google/makerspace-auth/docs/tool-connection/epilog_mini_24/plates/two_box_mount.png

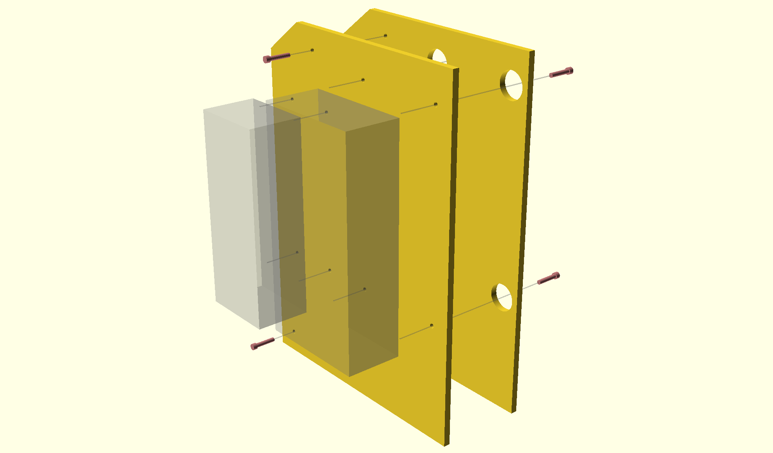
docs/tool-connection/epilog_mini_24/plates/two_box_mount.png
