google/makerspace-auth/docs/tool-connection/epilog_mini_24/plates/one_box_mount_inner.scad

include <one_box_mount_lib.scad>
Inner();
