google/makerspace-auth/docs/tool-connection/epilog_mini_24/plates/one_box_mount_lid_hole_template.scad

include <one_box_mount_lib.scad>
LidHoleTemplate();
