google/makerspace-auth/docs/tool-connection/epilog_mini_24/plates/two_box_mount_demo.scad

include <two_box_mount_lib.scad>
rotate([90,0,0]) Exploded();
