google/makerspace-auth/docs/tool-connection/epilog_mini_24/plates/two_box_mount_inner.scad

include <two_box_mount_lib.scad>
Inner();
