google/makerspace-auth/docs/tool-connection/epilog_mini_24/plates/two_box_mount_outer.scad

include <two_box_mount_lib.scad>
Outer();
