google/makerspace-auth/docs/tool-connection/epilog_mini_24/shelf/bracket_both.scad

include <bracket_lib.scad>
Main(hard_support=false);
MainClip();
