google/makerspace-auth/docs/tool-connection/epilog_mini_24/shelf/bracket_main.scad

include <bracket_lib.scad>
Main();
