google/makerspace-auth/software/authbox/tests/test_config.py

# Copyright 2017 Google Inc. All Rights Reserved.
#
# Licensed under the Apache License, Version 2.0 (the "License");
# you may not use this file except in compliance with the License.
# You may obtain a copy of the License at
#
#     http://www.apache.org/licenses/LICENSE-2.0
#
# Unless required by applicable law or agreed to in writing, software
# distributed under the License is distributed on an "AS-IS" BASIS,
# WITHOUT WARRANTIES OR CONDITIONS OF ANY KIND, either express or implied.
# See the License for the specific language governing permissions and
# limitations under the License.

"""Tests for authbox.config"""

import unittest

import authbox.config

from . import setup_mock_pin_factory  # noqa: F401


class ConfigTest(unittest.TestCase):
    def test_parse_time(self):
        cfg = authbox.config.Config
        # ints
        self.assertEqual(61, cfg.parse_time("61"))
        self.assertEqual(61, cfg.parse_time("61s"))
        self.assertEqual(90, cfg.parse_time("1m30s"))
        self.assertEqual(3660, cfg.parse_time("61m"))
        self.assertEqual(7200, cfg.parse_time("2h"))
        self.assertEqual(86400, cfg.parse_time("1d"))

        self.assertEqual(1.5, cfg.parse_time("1.5s"))
        self.assertEqual(4320, cfg.parse_time("1.2h"))
        self.assertRaises(Exception, cfg.parse_time, "")
        self.assertRaises(Exception, cfg.parse_time, "30x")

        self.assertEqual(5, cfg.parse_time(5))

    def test_get_int_seconds(self):
        c = authbox.config.Config(None)
        c._config.add_section("section")
        c._config.set("section", "a", "15m")
        self.assertEqual(15 * 60, c.get_int_seconds("section", "a", 999))

    def test_get_int_seconds_absent(self):
        c = authbox.config.Config(None)
        self.assertEqual(999, c.get_int_seconds("section", "a", 999))

    def test_get(self):
        c = authbox.config.Config(None)
        c._config.add_section("section")
        c._config.set("section", "a", "1{b}2")
        c._config.set("section", "b", "x")
        self.assertEqual("1x2", c.get("section", "a"))


class OneSectionConfig(object):
    def __init__(self, contents):
        self.contents = contents

    def get(self, section_name, key):
        if section_name == "section":
            return self.contents[key]


class RecursiveConfigParamLookupTest(unittest.TestCase):
    def test_simple(self):
        c = OneSectionConfig({"a": "b"})
        self.assertEqual(
            "abc", authbox.config.recursive_config_lookup("abc", c, "section")
        )
        self.assertEqual(
            "b", authbox.config.recursive_config_lookup("{a}", c, "section")
        )
        self.assertRaises(
            KeyError, authbox.config.recursive_config_lookup, "{x}", c, "section"
        )

    def test_simple_left_alone(self):
        c = OneSectionConfig({"a": "b"})
        self.assertEqual(
            "{0} b", authbox.config.recursive_config_lookup("{0} {a}", c, "section")
        )
        self.assertEqual(
            "{} b", authbox.config.recursive_config_lookup("{} {a}", c, "section")
        )

    def test_recursive(self):
        c = OneSectionConfig(
            {"a": "{b}{b}", "b": "{c}2", "c": "d", "broken": "{b2}", "b2": "{missing}"}
        )
        self.assertEqual(
            "d2d2", authbox.config.recursive_config_lookup("{a}", c, "section")
        )
        self.assertRaises(
            KeyError, authbox.config.recursive_config_lookup, "{broken}", c, "section"
        )

    def test_recursive_fail(self):
        c = OneSectionConfig({"a": "{b}", "b": "{a}"})
        self.assertRaises(
            authbox.config.CycleError,
            authbox.config.recursive_config_lookup,
            "{a}",
            c,
            "section",
        )
