google/makerspace-auth/software/authbox/tests/test_gpio_buzzer.py

# Copyright 2018 Google Inc. All Rights Reserved.
#
# Licensed under the Apache License, Version 2.0 (the "License");
# you may not use this file except in compliance with the License.
# You may obtain a copy of the License at
#
#     http://www.apache.org/licenses/LICENSE-2.0
#
# Unless required by applicable law or agreed to in writing, software
# distributed under the License is distributed on an "AS-IS" BASIS,
# WITHOUT WARRANTIES OR CONDITIONS OF ANY KIND, either express or implied.
# See the License for the specific language governing permissions and
# limitations under the License.

"""Tests for authbox.gpio_buzzer"""

import queue
import unittest

import authbox.gpio_buzzer
from authbox import fake_gpio_for_testing

from . import setup_mock_pin_factory  # noqa: F401


class TestBuzzer(authbox.gpio_buzzer.Buzzer):
    def assert_states(self, expected_states):
        assert len(self.gpio_buzzer.pin.states) == len(expected_states)
        self.gpio_buzzer.pin.assert_states(expected_states)

    def clear_states(self):
        self.gpio_buzzer.pin.clear_states()

    def close(self):
        self.gpio_buzzer.close()


class BuzzerTest(unittest.TestCase):
    def setUp(self):
        self.time = fake_gpio_for_testing.FakeTime()
        authbox.gpio_buzzer.time = self.time

        self.q = queue.Queue()
        self.b = TestBuzzer(self.q, "b", "15")
        self.b.clear_states()

    def tearDown(self):
        self.b.close()

    def test_on(self):
        self.time.sleep(2)
        self.b.on()
        self.b.run_inner(False)
        self.assertRaises(queue.Empty, self.b.run_inner, False)
        self.b.assert_states([False, True])

    def test_off(self):
        self.time.sleep(2)
        self.b.off()
        self.b.run_inner(False)
        self.assertRaises(queue.Empty, self.b.run_inner, False)
        self.b.assert_states([False])

    def test_beep(self):
        self.b.beep()
        self.b.run_inner(False)
        self.b.on()
        self.b.run_inner(False)
        self.assertRaises(queue.Empty, self.b.run_inner, False)
        self.b.assert_states([False, True, False, True])

    # BEEPING mode is not very testable, due to the infinite loop and empty
    # check.  We could put this in another thread, but that's a test for another
    # day...
    # def test_beeping(self):
    #  self.b.beepbeep()
    #  self.b.off(clear=False)  # Unusual, but avoids races in test.
    #  self.b.run_inner(False)
    #  # Queue is not empty.
    #  self.fake.compare_log([
    #      (0, 1, False), (0.3, 1, True), (0.6, 1, False)])
